petercpark/The_Uni/Pics/gregg stenokeyboards black.png

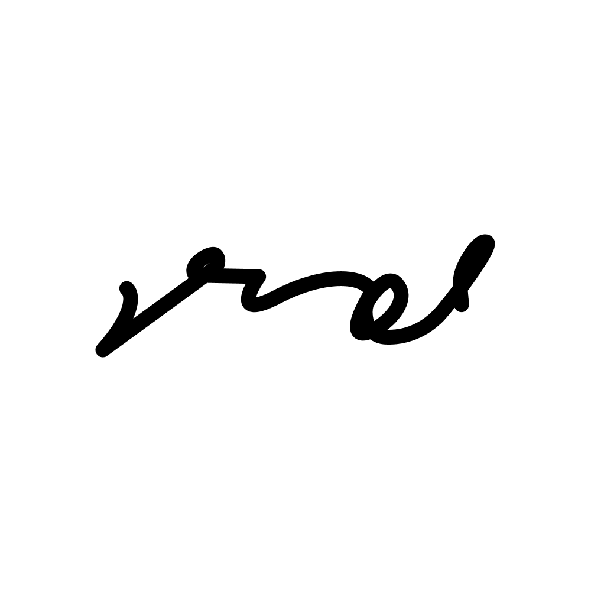
Pics/gregg stenokeyboards black.png
