petercpark/The_Uni/Pics/gregg stenokeyboards.png

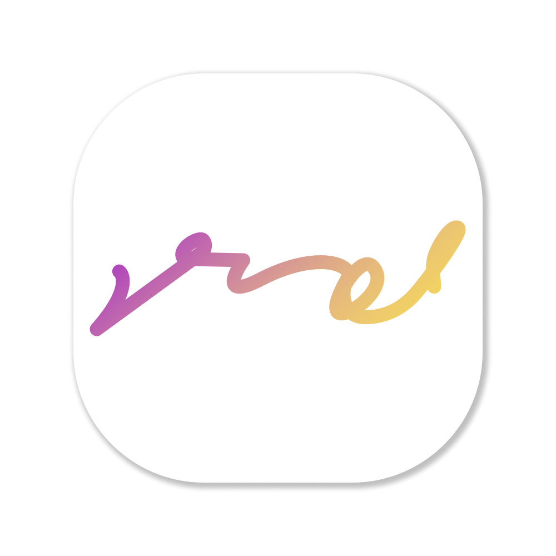
Pics/gregg stenokeyboards.png
