petercpark/The_Uni/Pics/gregg uni black.png

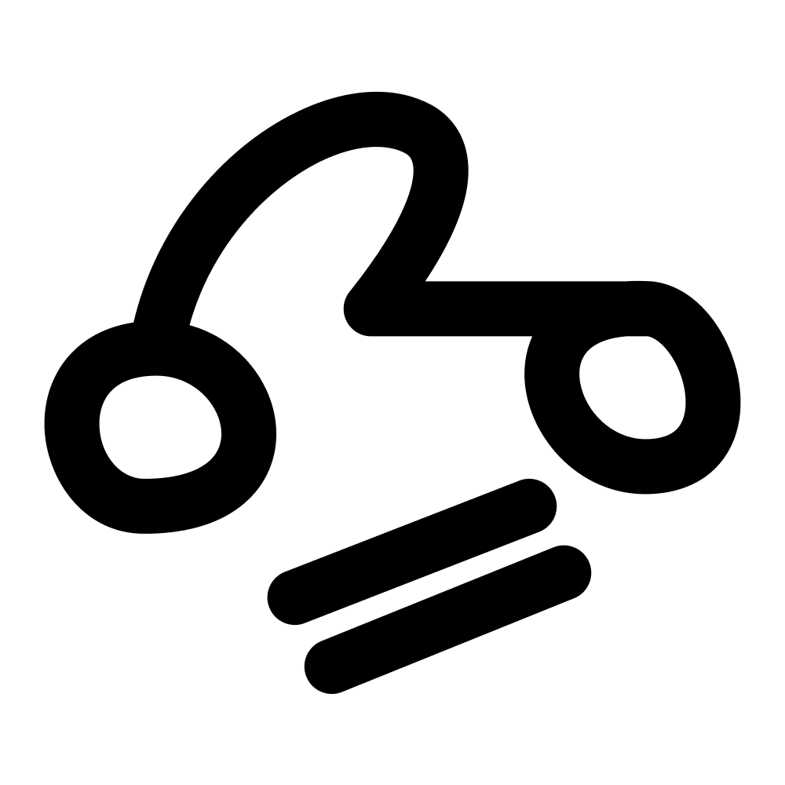
Pics/gregg uni black.png
