petercpark/The_Uni/Pics/keycap.jpg

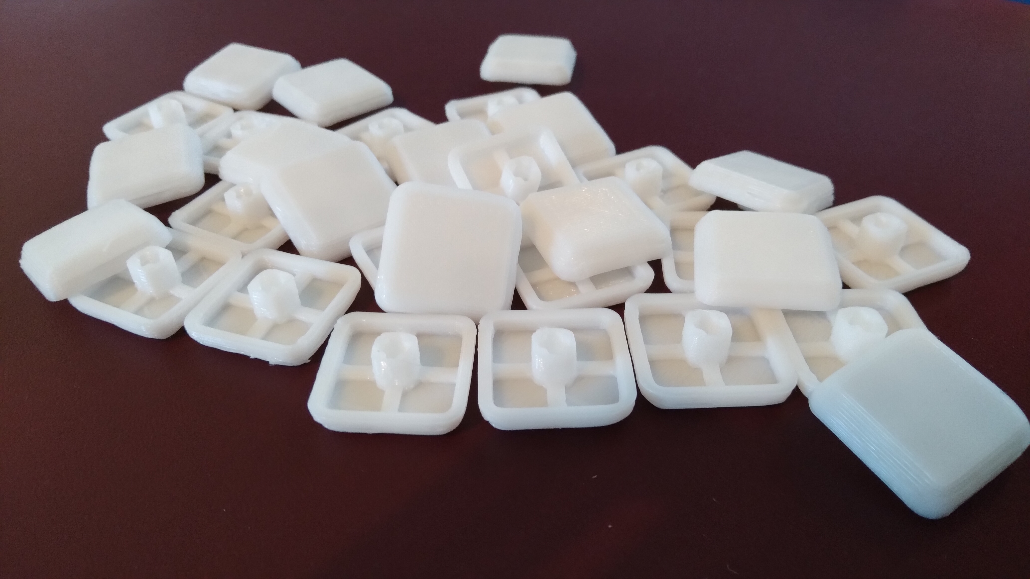
Pics/keycap.jpg
