petercpark/The_Uni/Pics/pro-micro-on-uni.jpg

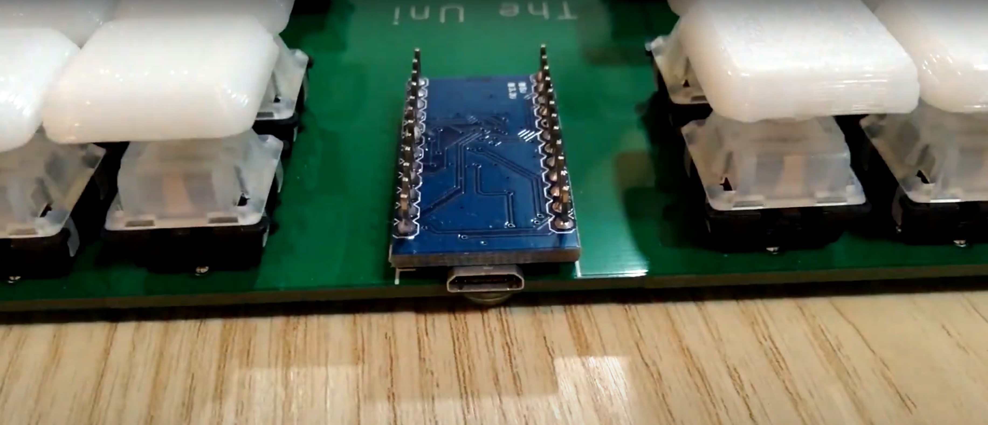
Pics/pro-micro-on-uni.jpg
