petercpark/The_Uni/Pics/rubber-feet.jpg

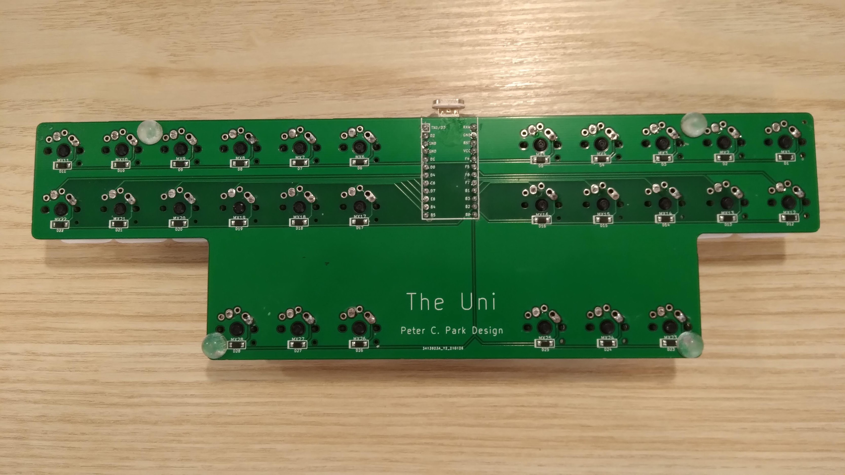
Pics/rubber-feet.jpg
