petercpark/The_Uni/Pics/the uni in gregg shorthand.png

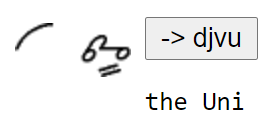
Pics/the uni in gregg shorthand.png
