petercpark/The_Uni/Pics/uni board render.png

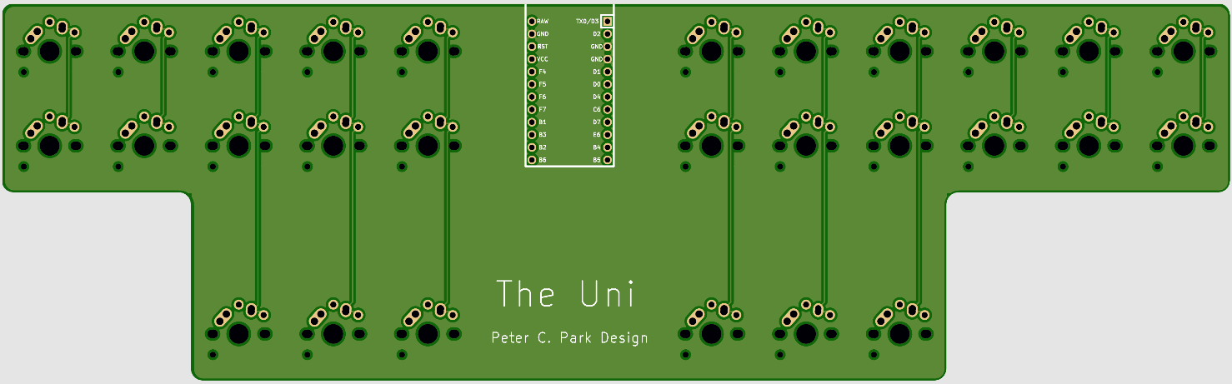
Pics/uni board render.png
