petercpark/The_Uni/Pics/uni v2/backplate/20210516_214459.jpg

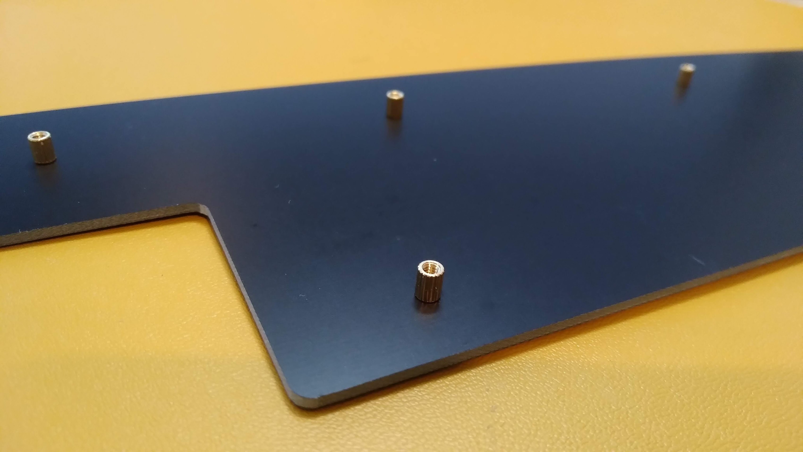
Pics/uni v2/backplate/20210516_214459.jpg
