petercpark/The_Uni/Pics/uni v2/backplate/20210516_231722.jpg

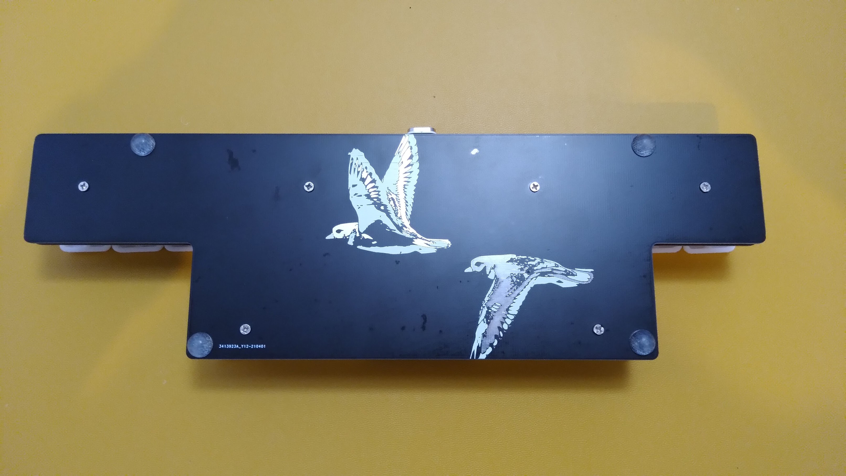
Pics/uni v2/backplate/20210516_231722.jpg
