petercpark/The_Uni/Pics/uni v2/backplate/IMG_9128.JPG

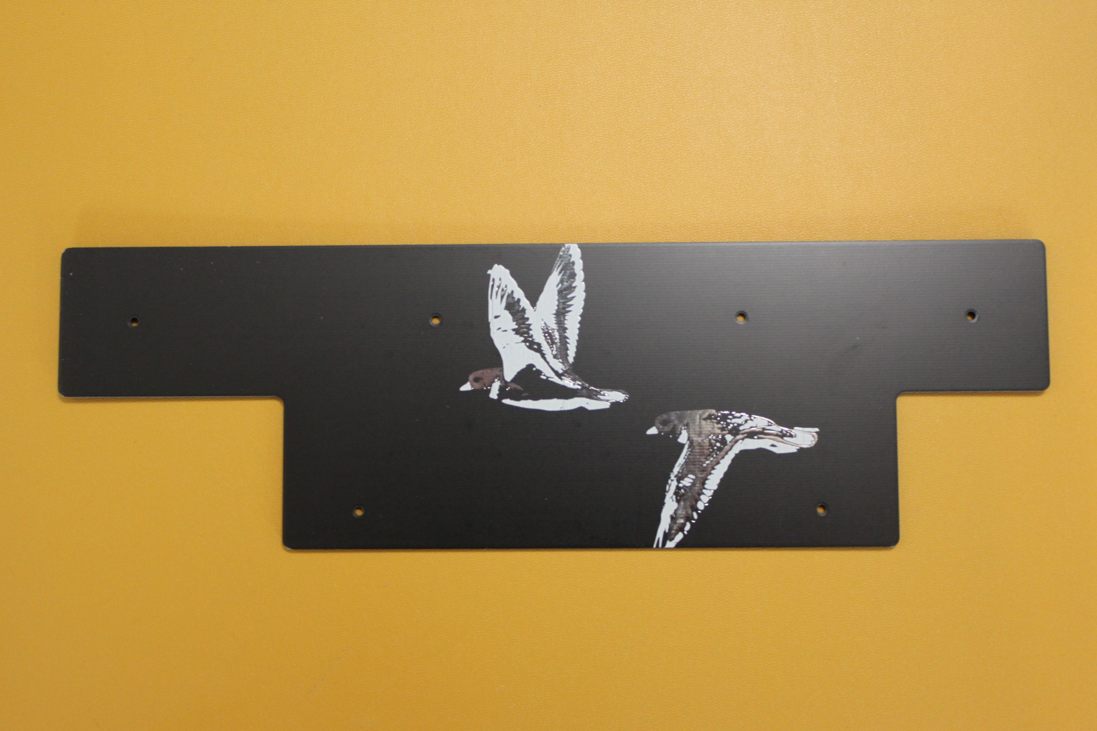
Pics/uni v2/backplate/IMG_9128.JPG
