petercpark/The_Uni/Pics/uni v2/backplate/IMG_9129.JPG

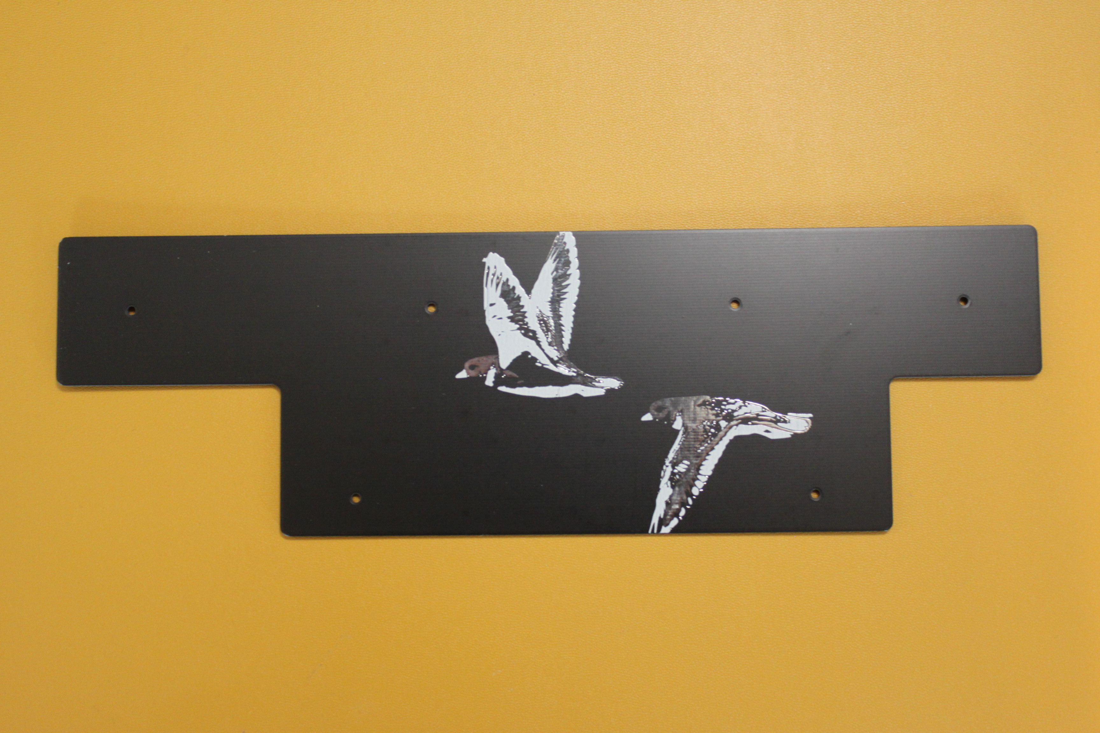
Pics/uni v2/backplate/IMG_9129.JPG
