petercpark/The_Uni/Pics/uni v2/backplate/IMG_9130.JPG

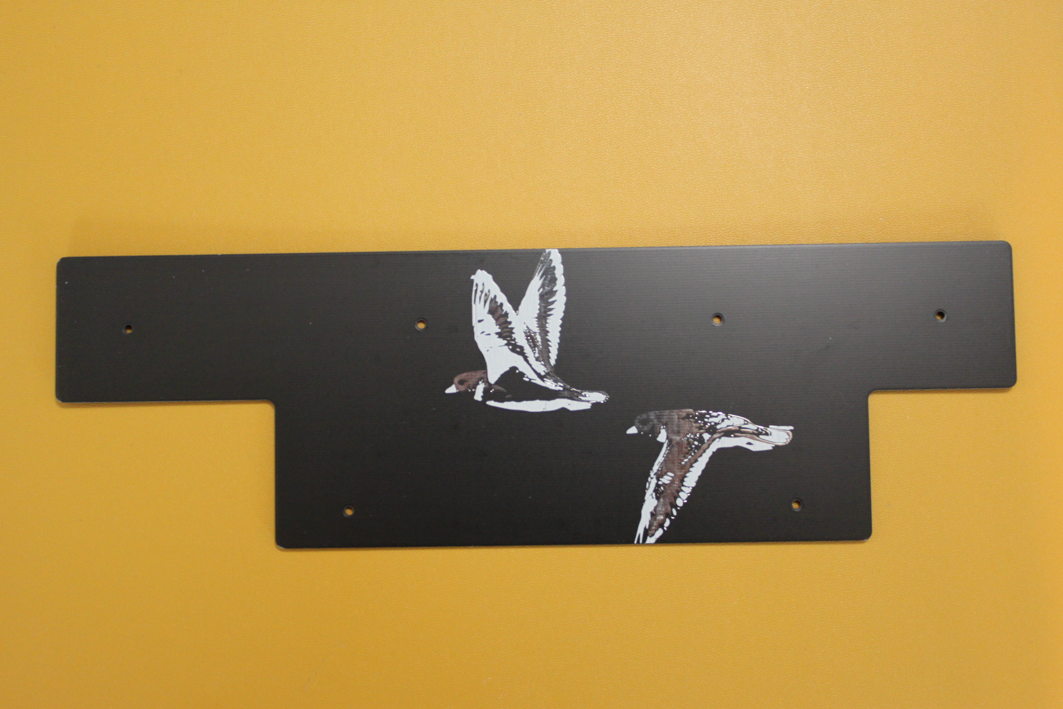
Pics/uni v2/backplate/IMG_9130.JPG
