petercpark/The_Uni/Pics/uni v2/IMG_9068.JPG

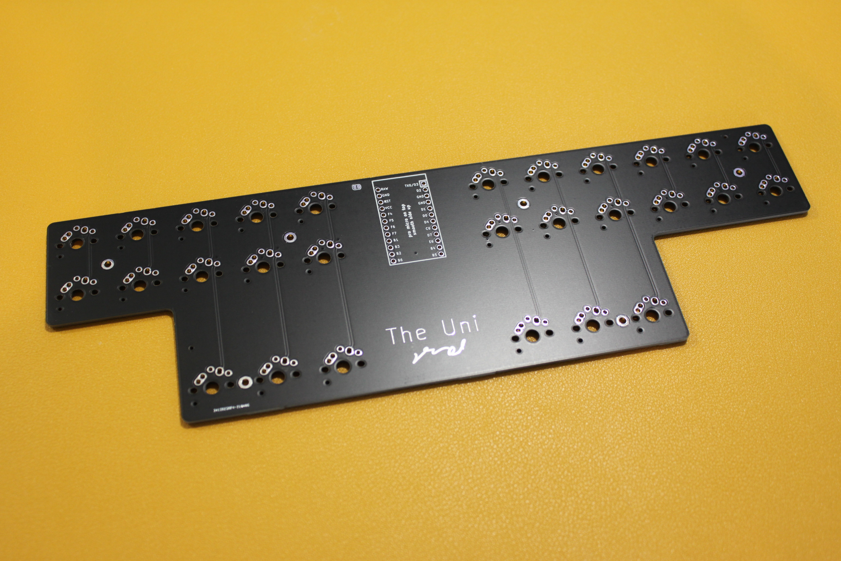
Pics/uni v2/IMG_9068.JPG
