petercpark/The_Uni/Pics/uni v2/IMG_9070.JPG

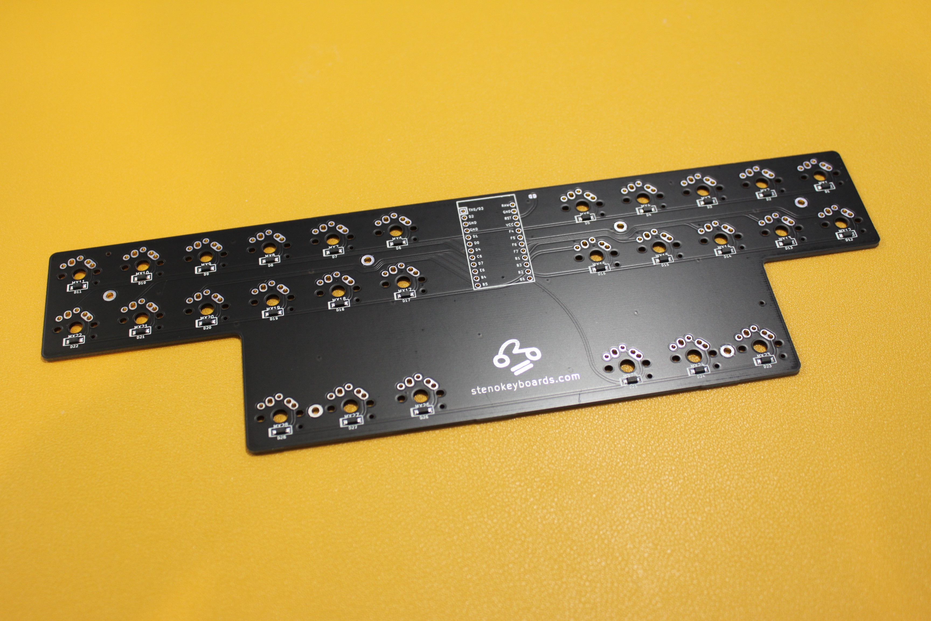
Pics/uni v2/IMG_9070.JPG
