petercpark/The_Uni/Pics/uni v2/IMG_9071.JPG

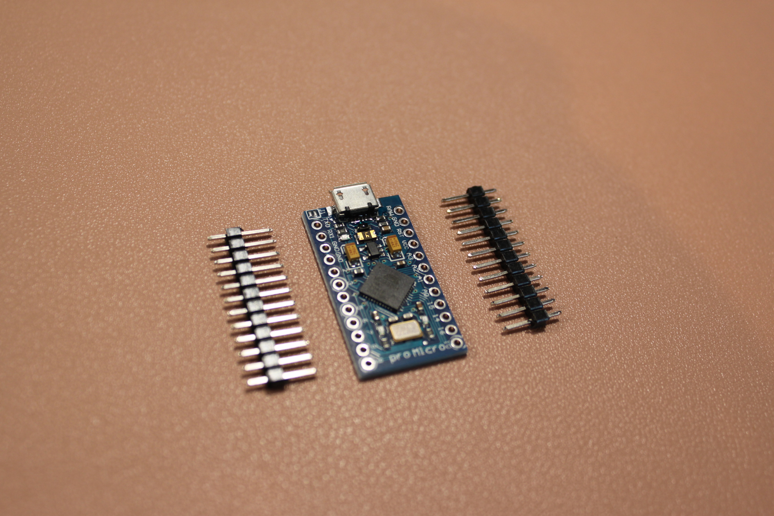
Pics/uni v2/IMG_9071.JPG
