petercpark/The_Uni/Pics/uni v2/IMG_9076.JPG

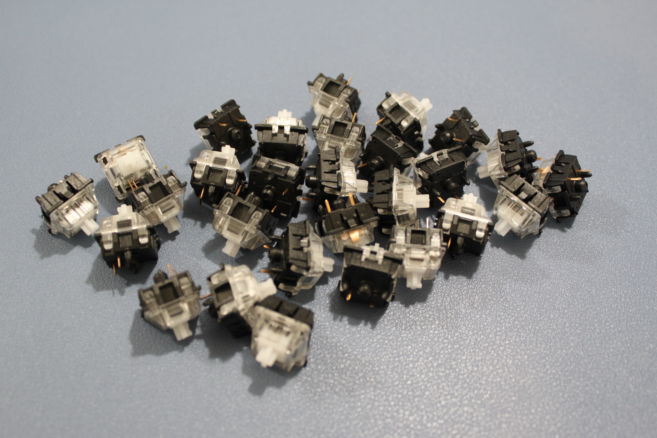
Pics/uni v2/IMG_9076.JPG
