petercpark/The_Uni/Pics/uni v2/IMG_9077.JPG

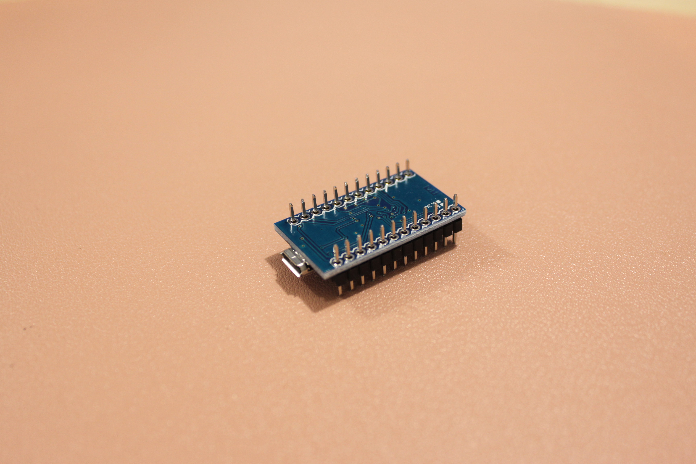
Pics/uni v2/IMG_9077.JPG
