petercpark/The_Uni/Pics/uni v2/IMG_9079.JPG

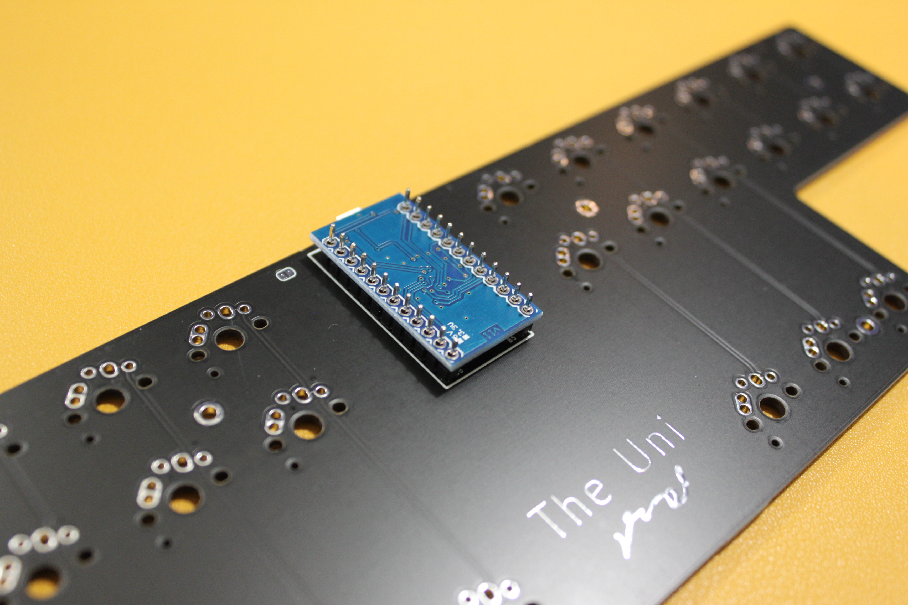
Pics/uni v2/IMG_9079.JPG
