petercpark/The_Uni/Pics/uni v2/IMG_9083.JPG

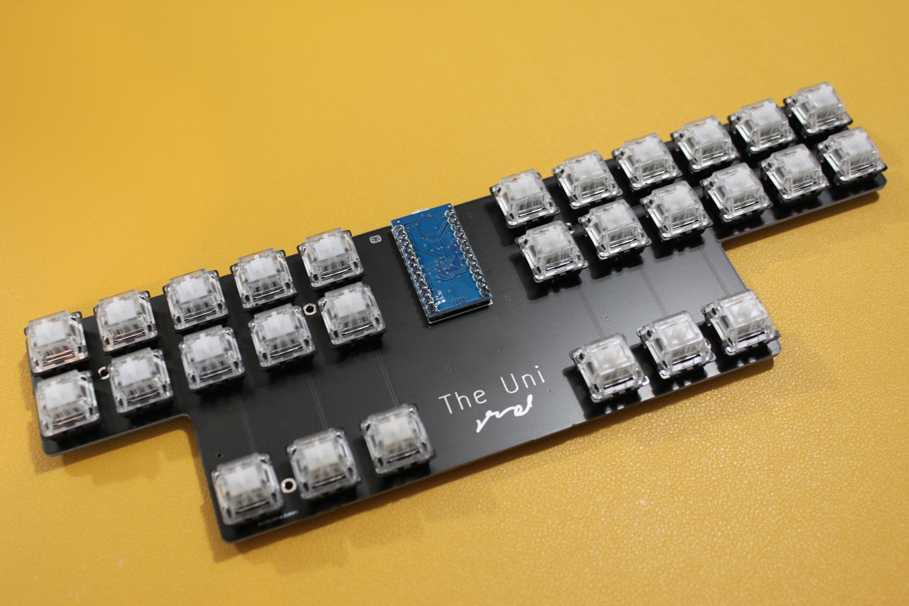
Pics/uni v2/IMG_9083.JPG
