petercpark/The_Uni/Pics/uni v2/IMG_9085.JPG

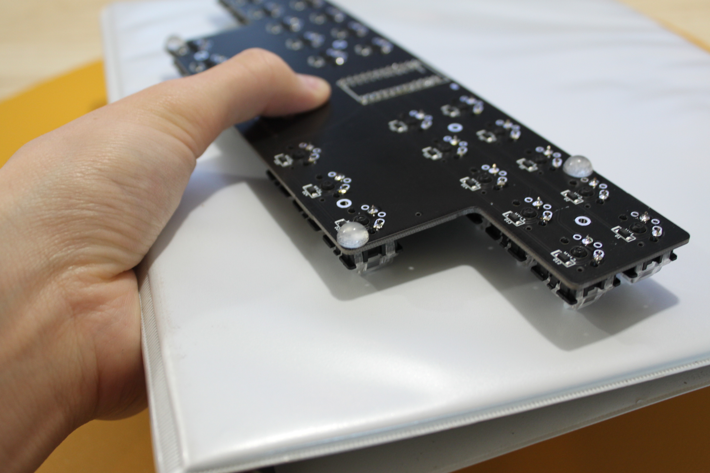
Pics/uni v2/IMG_9085.JPG
