petercpark/The_Uni/Pics/uni v2/IMG_9087.JPG

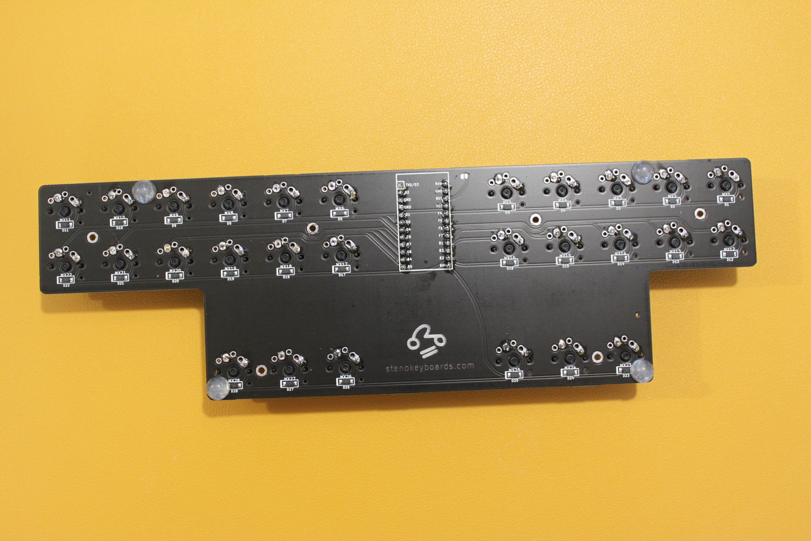
Pics/uni v2/IMG_9087.JPG
