petercpark/The_Uni/Pics/uni v2/IMG_9091 edit.jpg

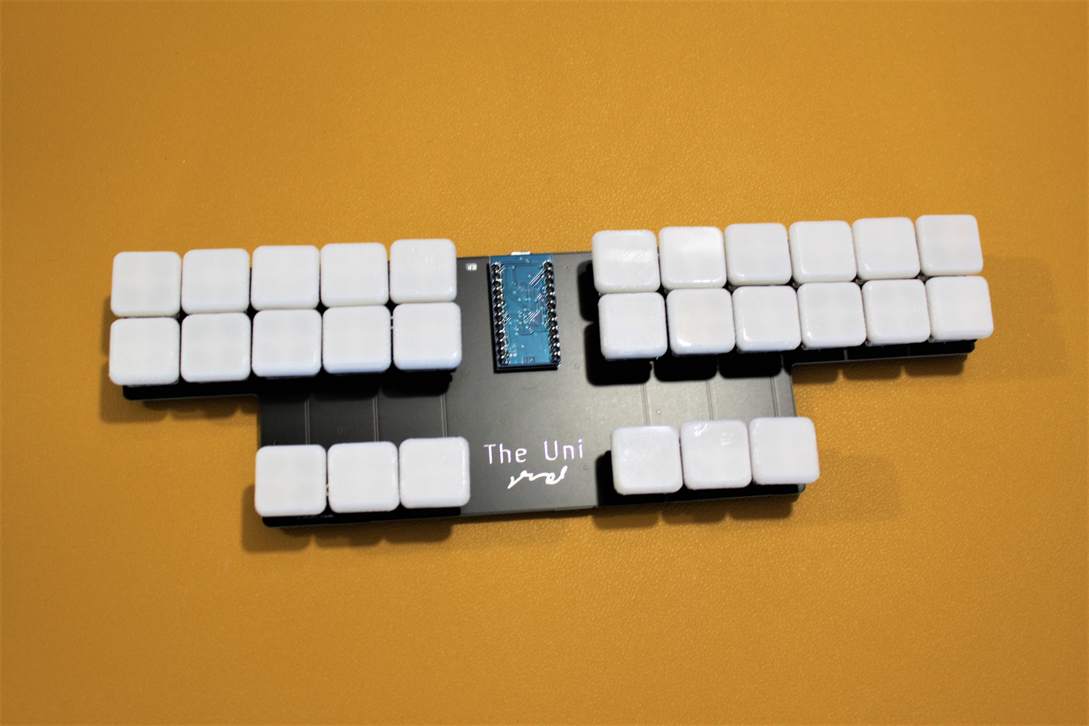
Pics/uni v2/IMG_9091 edit.jpg
