petercpark/The_Uni/Pics/uni v2/IMG_9093.JPG

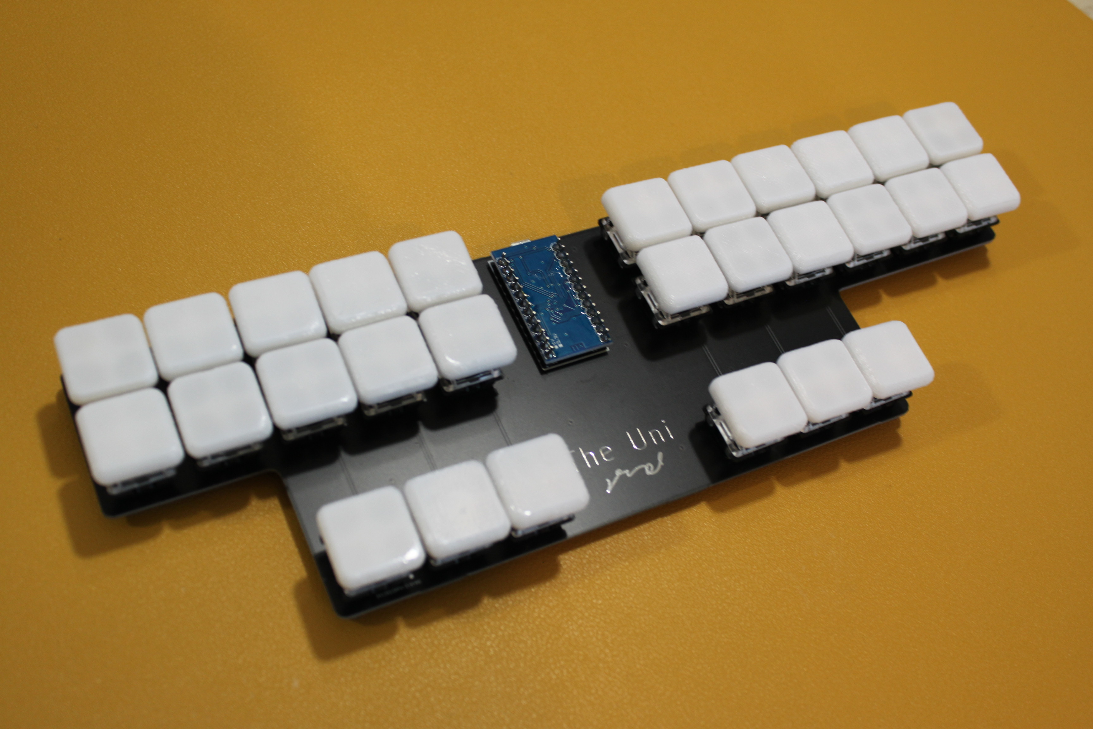
Pics/uni v2/IMG_9093.JPG
