petercpark/The_Uni/Pics/uni v2/IMG_9097.JPG

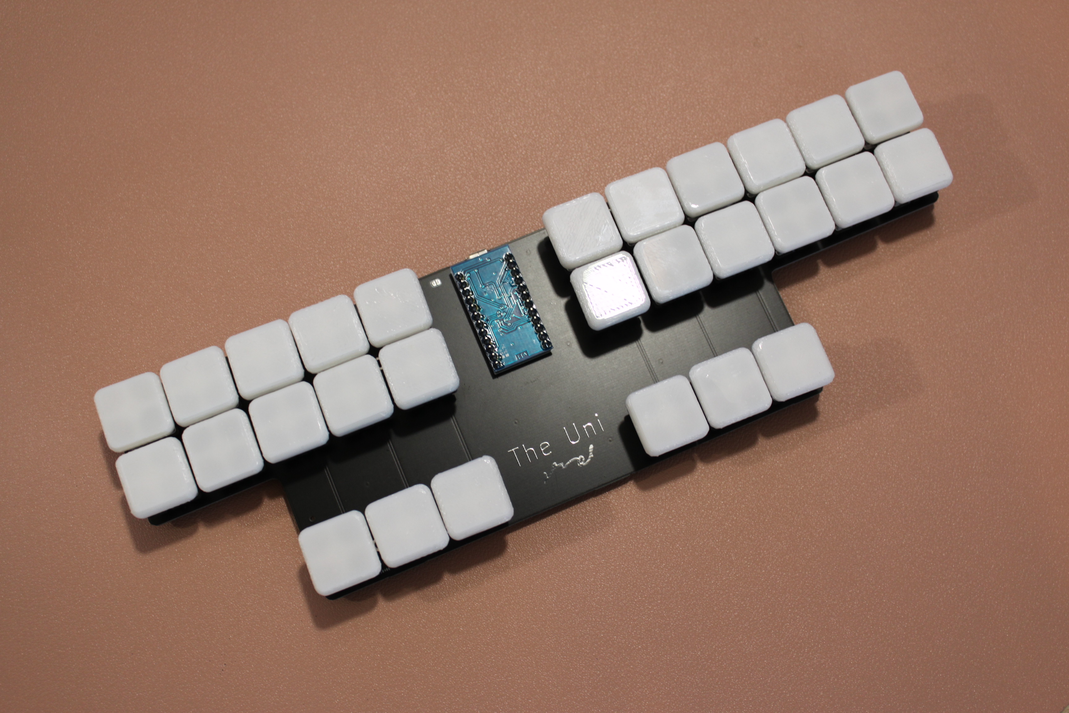
Pics/uni v2/IMG_9097.JPG
