petercpark/The_Uni/Pics/uni v2/IMG_9100.JPG

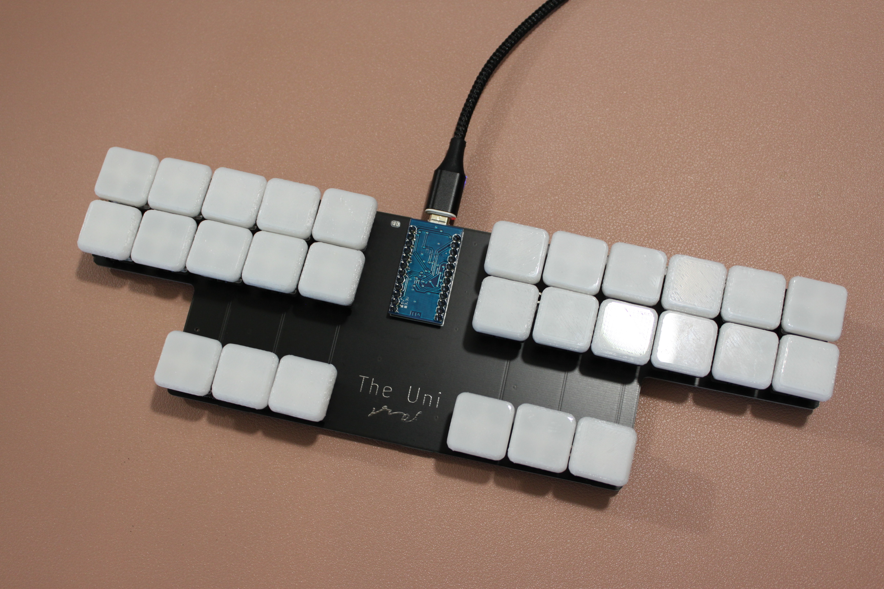
Pics/uni v2/IMG_9100.JPG
