petercpark/The_Uni/Pics/uni v2/IMG_9119.JPG

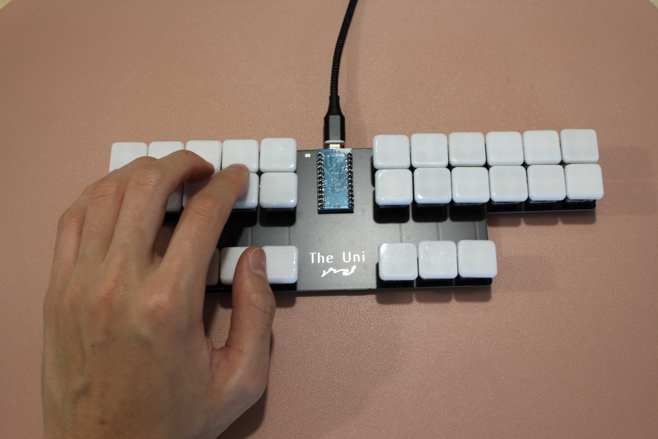
Pics/uni v2/IMG_9119.JPG
