petercpark/The_Uni/Pics/uni v2/reset pad.png

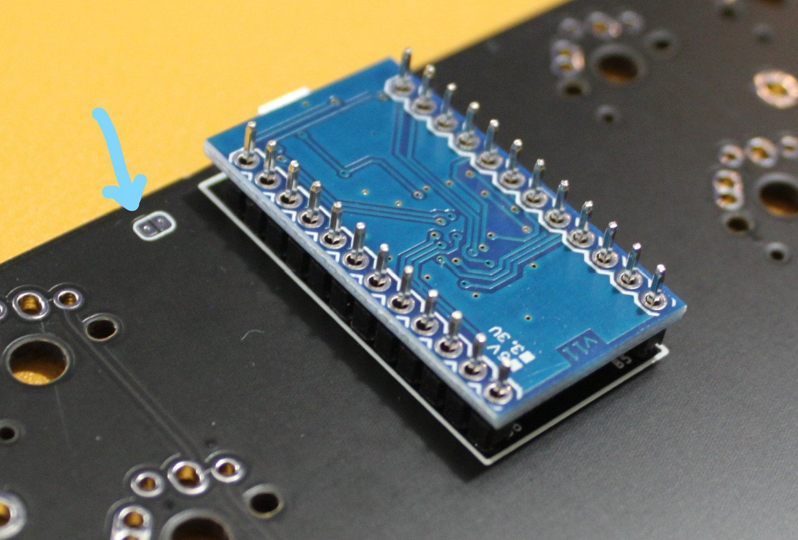
Pics/uni v2/reset pad.png
