petercpark/The_Uni/Pics/uni-on-table.jpg

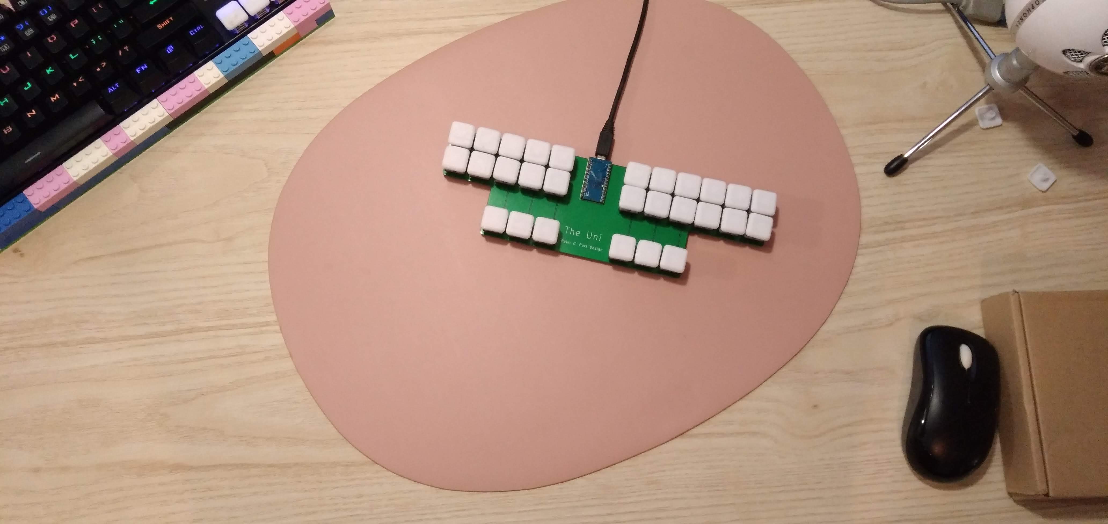
Pics/uni-on-table.jpg
