petercpark/The_Uni/Pics/uni-pcb.jpg

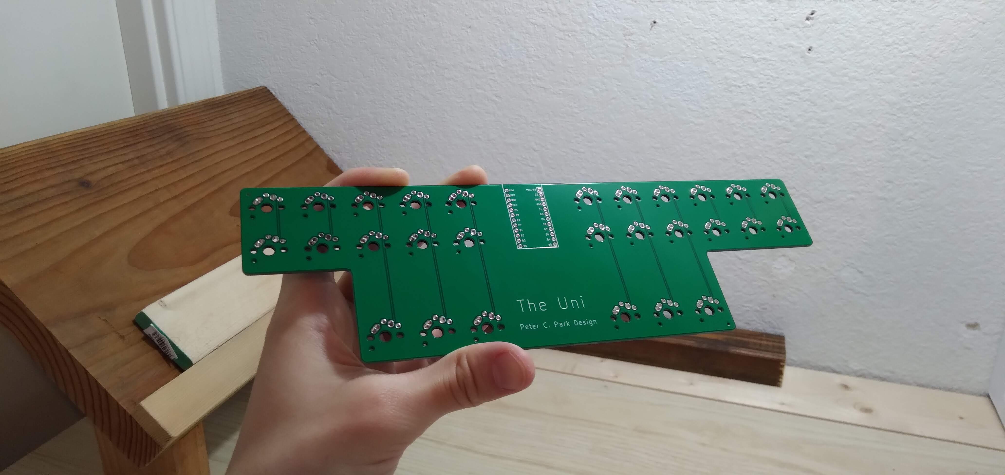
Pics/uni-pcb.jpg
