petercpark/The_Uni/Pics/uni-v2-render-back.png

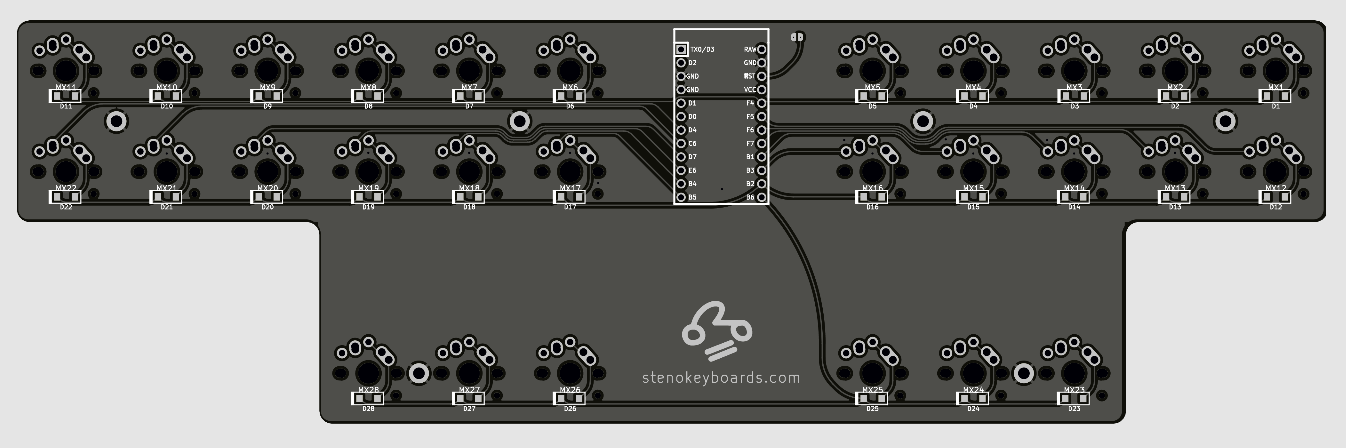
Pics/uni-v2-render-back.png
