petercpark/The_Uni/3d Printed Keycaps/cherry mount.png

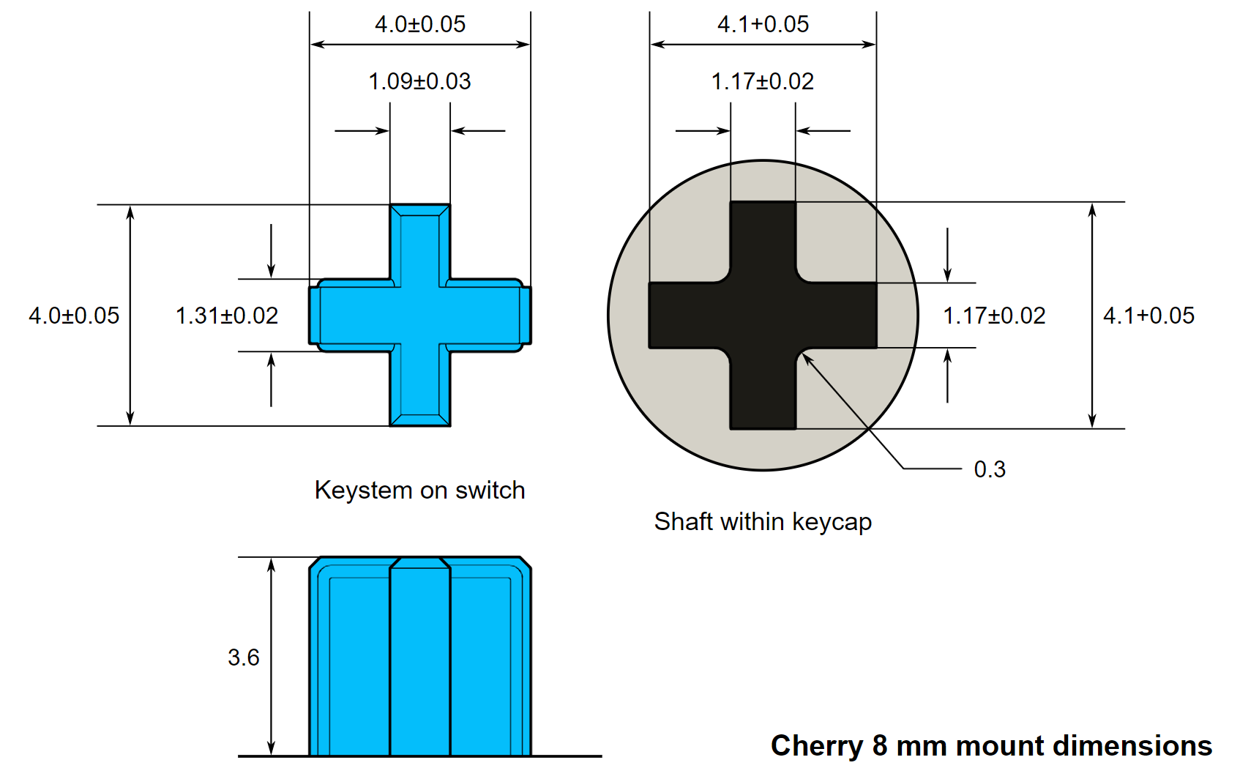
3d Printed Keycaps/cherry mount.png
