petercpark/The_Uni/3d Printed Keycaps/keycap diagram.png

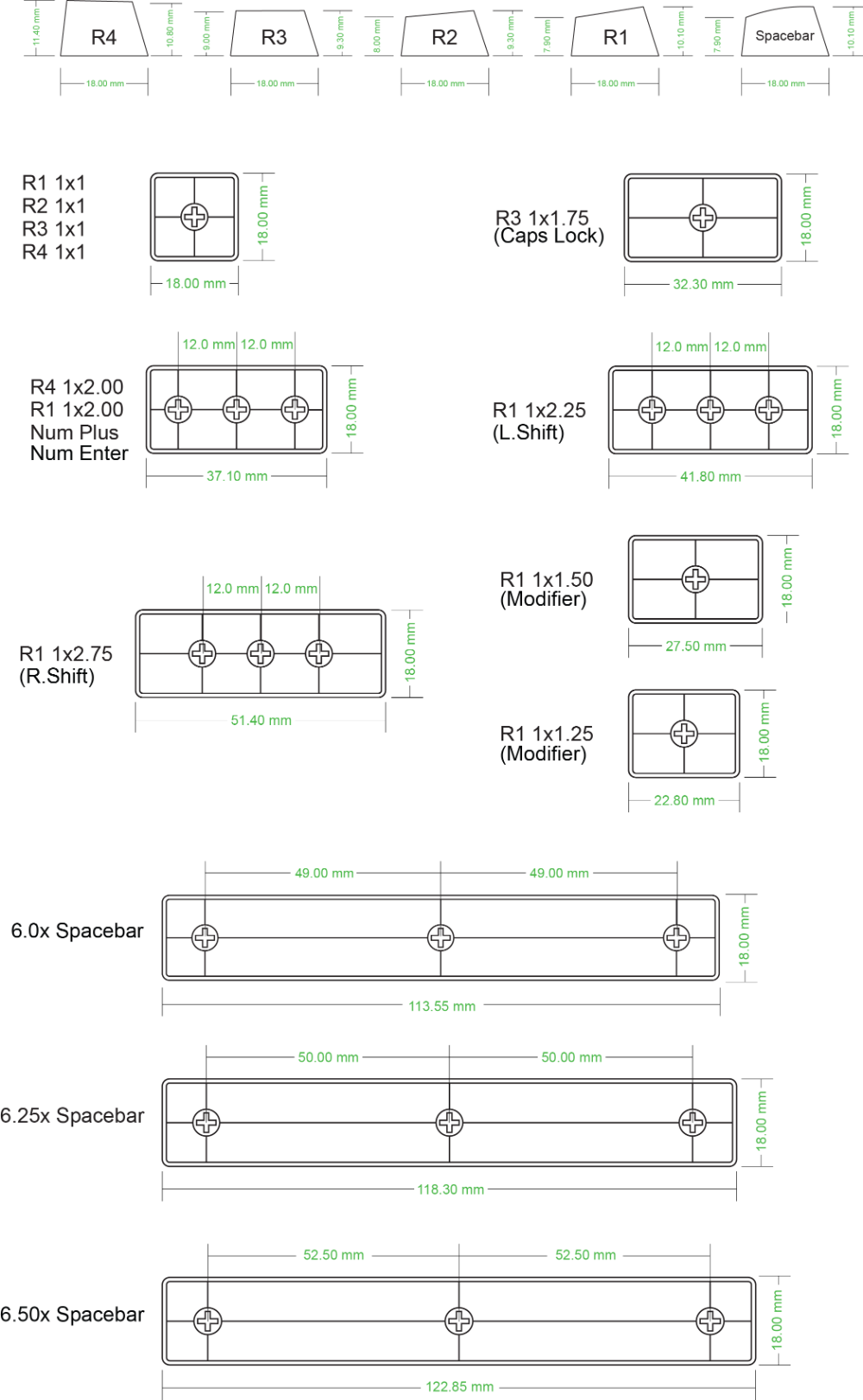
3d Printed Keycaps/keycap diagram.png
