petercpark/The_Uni/Pics/single-3d-printed-keycap.jpg

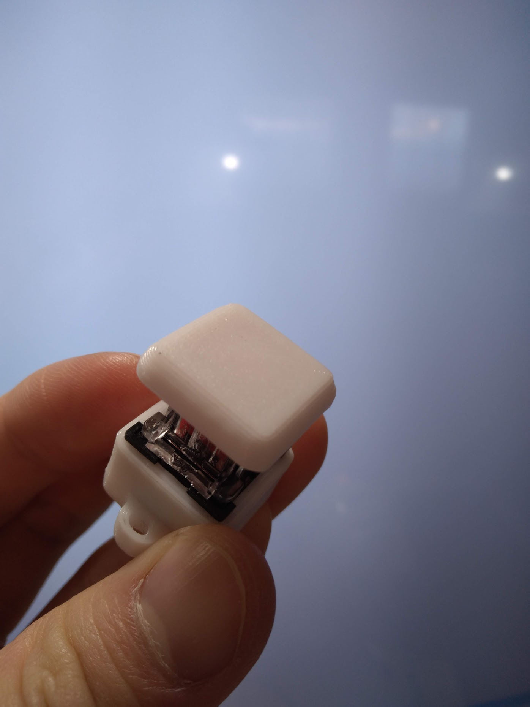
Pics/single-3d-printed-keycap.jpg
