petercpark/The_Uni/Pics/uni build pics/Flatwater#4199.jpg

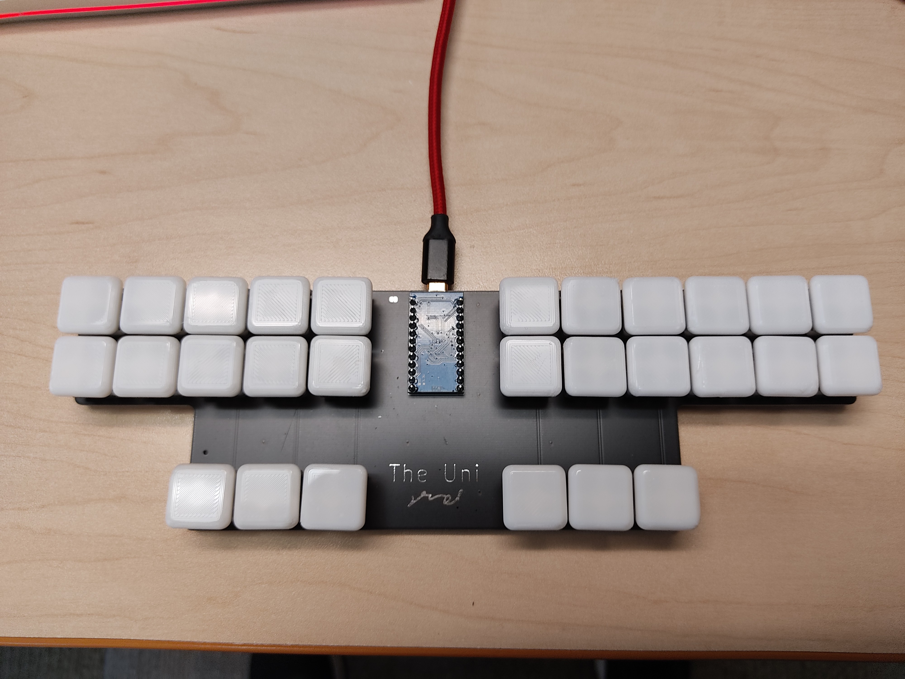
Pics/uni build pics/Flatwater#4199.jpg
